catphish/flex-floppy/util.c

#include <stm32l433xx.h>

void usleep(unsigned int delay) {
  SysTick->LOAD = 0x00FFFFFF;
  SysTick->VAL = 0;
  SysTick->CTRL = 5;
  while(0x00FFFFFF - SysTick->VAL < delay * 80);
}

void msleep(unsigned int delay) {
	for(int n=0; n<delay; n++) {
		usleep(1000);
	}
}
